dangrie158/USB-Power-Meter/3D Model/eagleUp_Board V1_board_bottom.png

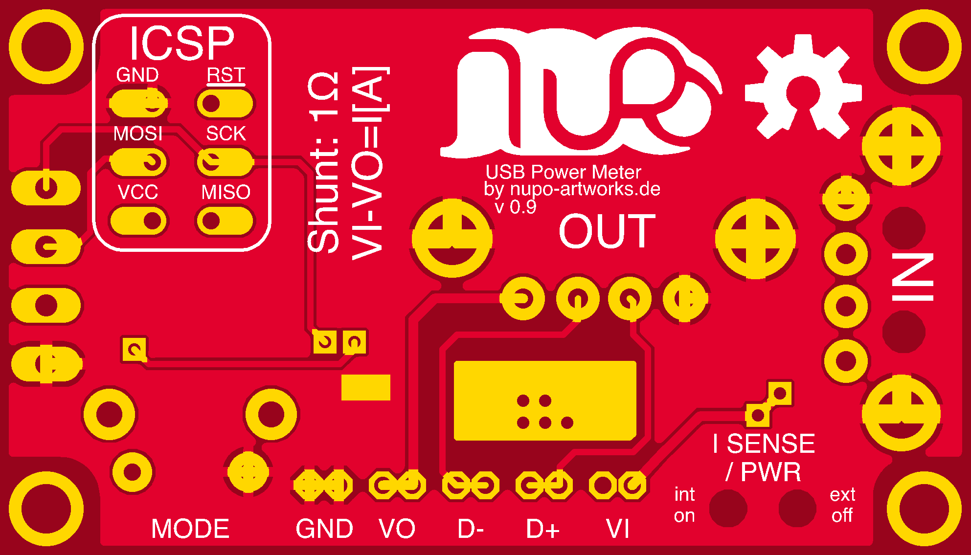
3D Model/eagleUp_Board V1_board_bottom.png
