dangrie158/USB-Power-Meter/3D Model/eagleUp_Board V1_board_top.png

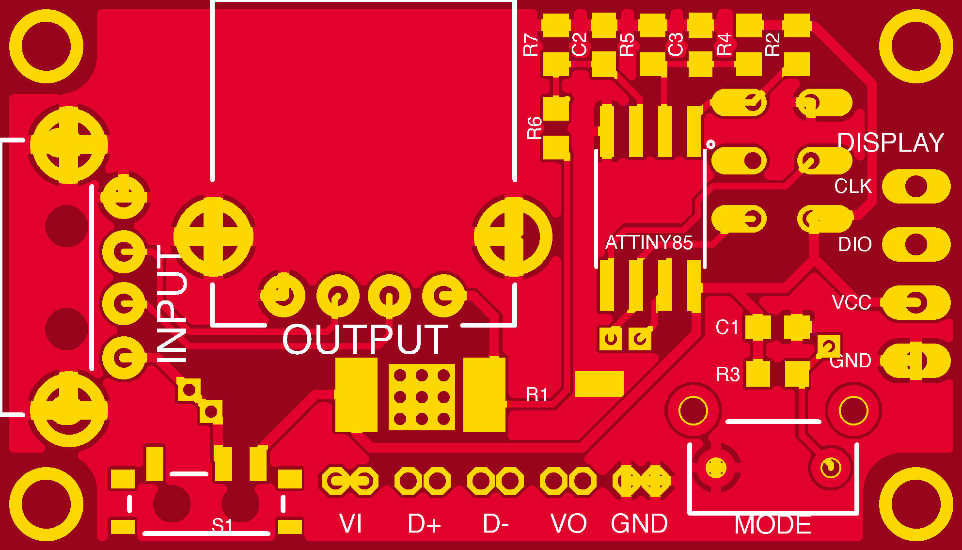
3D Model/eagleUp_Board V1_board_top.png
