dangrie158/USB-Power-Meter/3D Model/eagleUp_Board V1_outline.png

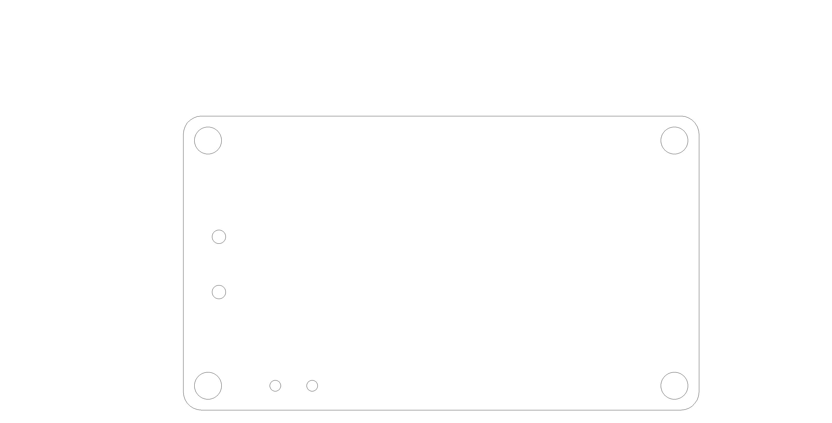
3D Model/eagleUp_Board V1_outline.png
